nushackers/hnr26-badge-quacknroll/firmware/filesystem/boot.py

# This file is executed on every boot (including wake-boot from deepsleep)
#import esp
#esp.osdebug(None)
#import webrepl
#webrepl.start()

from app.main import * # Comment to stop badge program from running
